re-innovation/relogger/relogger_Overview/GSM Equipment/GSM SIM900/Blog Post Photos/ArduinoText.jpg

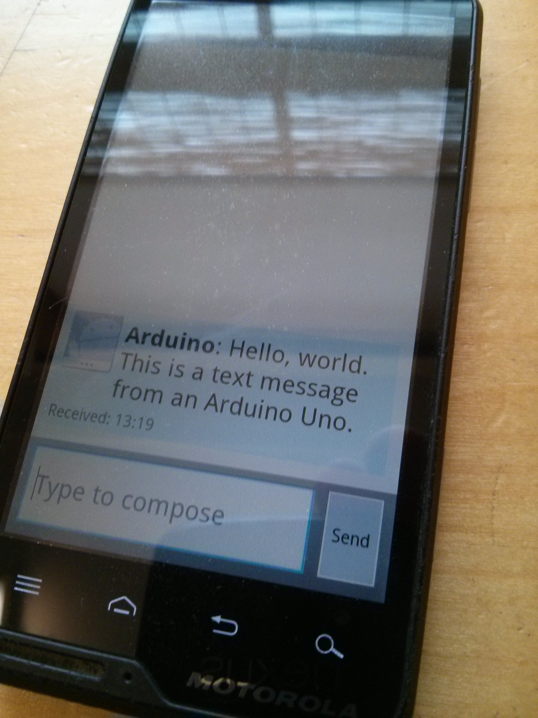
relogger_Overview/GSM Equipment/GSM SIM900/Blog Post Photos/ArduinoText.jpg
