re-innovation/relogger/relogger_Overview/GSM Equipment/GSM SIM900/Blog Post Photos/IMG_20141029_151024.jpg

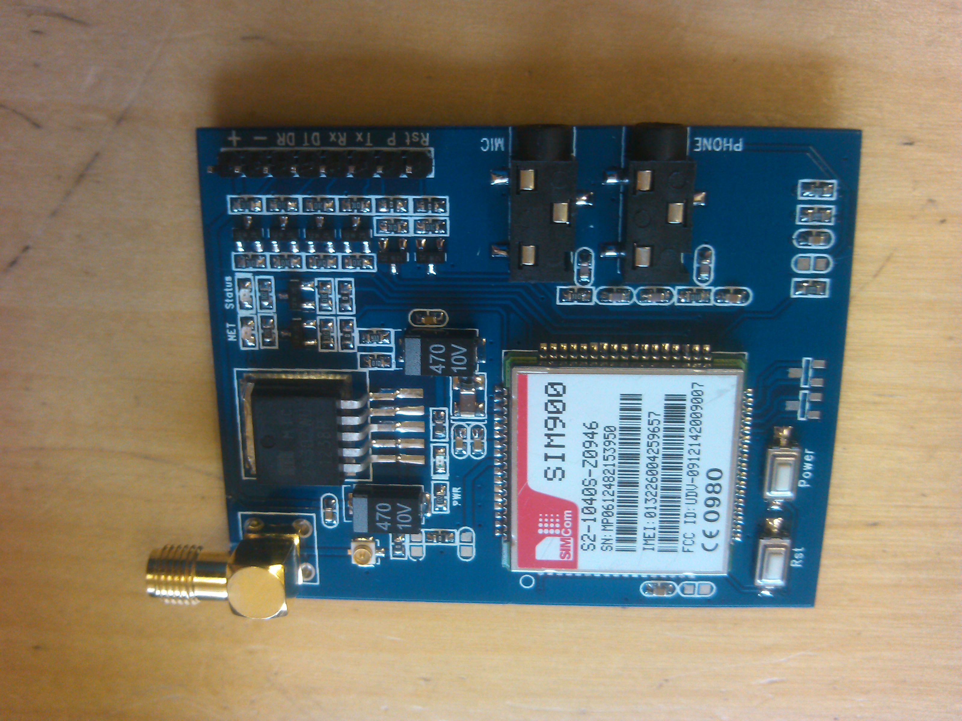
relogger_Overview/GSM Equipment/GSM SIM900/Blog Post Photos/IMG_20141029_151024.jpg
