re-innovation/relogger/relogger_Overview/GSM Equipment/GSM SIM900/Blog Post Photos/IMG_20141029_151031.jpg

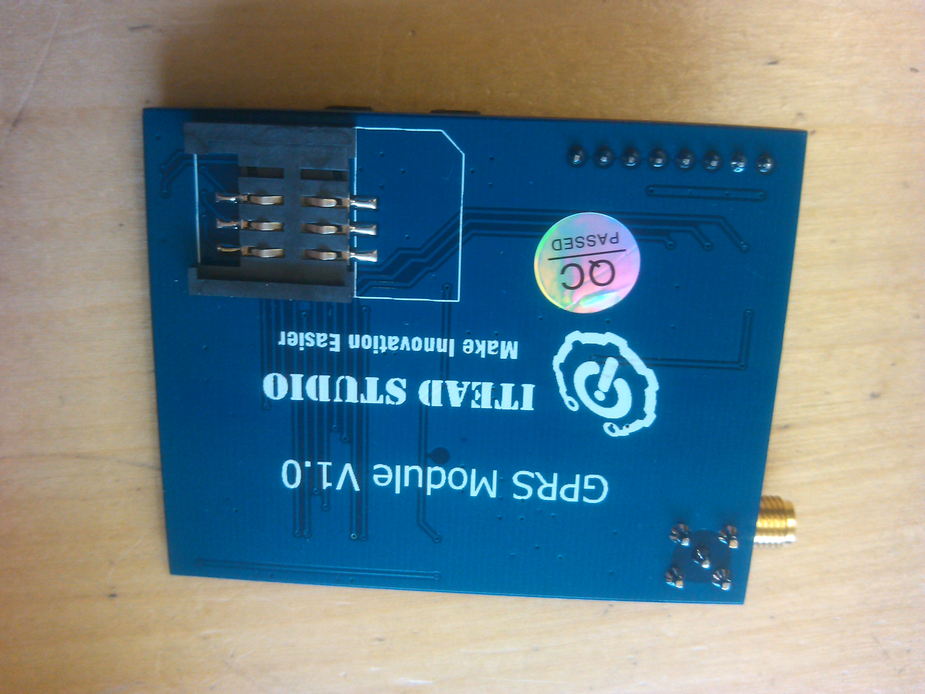
relogger_Overview/GSM Equipment/GSM SIM900/Blog Post Photos/IMG_20141029_151031.jpg
