re-innovation/relogger/relogger_Overview/Weather Monitoring/Humidity/Humidity RH11/TestHumidity1.png

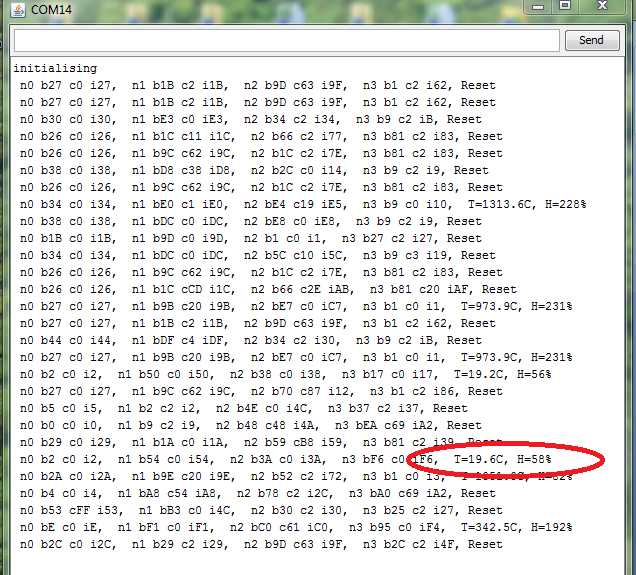
relogger_Overview/Weather Monitoring/Humidity/Humidity RH11/TestHumidity1.png
